BoujeeEnjinia1701/fieldnode/cad/drawings/FND-DWG-001.pdf

CONCEPT, NOT FOR FABRICATION | FieldNode · github.com/BoujeeEnjinia1701/fieldnode

FRONT VIEW
Scale 1:10; looking at the front (along +Y)

TOP VIEW
Scale 1:10; looking down (along -Z)

RIGHT VIEW
Scale 1:10; looking at the right side (along -X)

290

232 750

PRELIMINARY, NOT FOR FABRICATION

200

250 clamps

150

290 panel

915 MHZ WHIP (9)

PORTS A (LEFT) AND B, M12 5-PIN (10)

2 x M16 GLANDS (3)

POLE AXIS, 48.3 OD (40 TO 60)

NODE FACES -Y (TOWARD THE EQUATOR)

90

456

PANEL TILT 40 DEG

ISOMETRIC VIEW
Not to scale; grey pole stub is site supplied; seen from the front right and above, about 30 deg elevation

MAIN DIMENSIONS AND INTERFACES (MM)
Enclosure IP65 150 x 90 x 200 (W x D x H); base 1,750 above ground Panel 6 W 9 V class, 290 x 200, tilt 40 deg; top 2,206 above ground Panel overhangs lid by 57; front edge 121 above enclosure
Back plate 180 x 320 x 3 Al; V-blocks 60 x 33 x 20, 90 deg V
Band clamps 12 wide, 250 apart; poles 40 to 60 OD
Bracket bar 20 x 3: posts 161, struts 129 between holes Enclosure on 4 lugs, M5; bracket on 30 x 30 x 3 angle clips, M6
Bottom face: 2 rows, 27 and 55 in from the back face
Whip 915 MHz (US915), 190 long; tip 1,540 above ground
Option (14), not shown: shield 181 x 106 x 206, 15 gap, 4 thumb screws Ports A and B (10), M12 5-pin A-coded, pin positions per maker:
1 switched rail, 2 data A, 3 ground, 4 data B, 5 analog
Serial header (7) on the power board, pins 48 in from box front (lid off) Third-angle; front view from -Y; pole on Z axis; (n) = BOM line
REV | DESCRIPTION | DATE | BY
P1 | Preliminary GA for TRL 3 (from cad/src/model.py) | 2026-09-25 | AC
P2 | FND-DDR-002: 9 V class panel; sun shield option (14) | 2026-09-25 | AC
P3 | FND-DDR-003: design for construction | 2026-09-30 | AC
P4 | Port pinout, programming header (7), 915 MHz whip | 2026-10-02 | AC
FIELDNODE | github.com/BoujeeEnjinia1701/fieldnode

## General arrangement

DRAWING NO.
FND-DWG-001

REV
P4

SHEET
1 of 1

SIZE

## ANSI B

SCALE
1:10

UNITS
mm
PROJECTION | DATE
2026-10-02

DRAWN
Amish Chadha

MATERIAL / NOTES
Bought-in parts per bom/bom.csv; aluminium bracket and plate. PRELIMINARY, NOT FOR FABRICATION
Licensed CERN-OHL-S-2.0 · Design Molecule Lab · designmolecule.com | Generated from cad/src; do not edit by hand
