BoujeeEnjinia1701/fieldnode/cad/drawings/FND-DWG-101.pdf

### BUILD PLAN SKETCH, PLAN NOT YET BUILT FieldNode · github.com/BoujeeEnjinia1701/fieldnode

FRONT VIEW
Scale 1:5; looking at the front (along +Y)

TOP VIEW
Scale 1:5; looking down (along -Z)

RIGHT VIEW
Scale 1:5; looking at the right side (along -X)

180

3 320

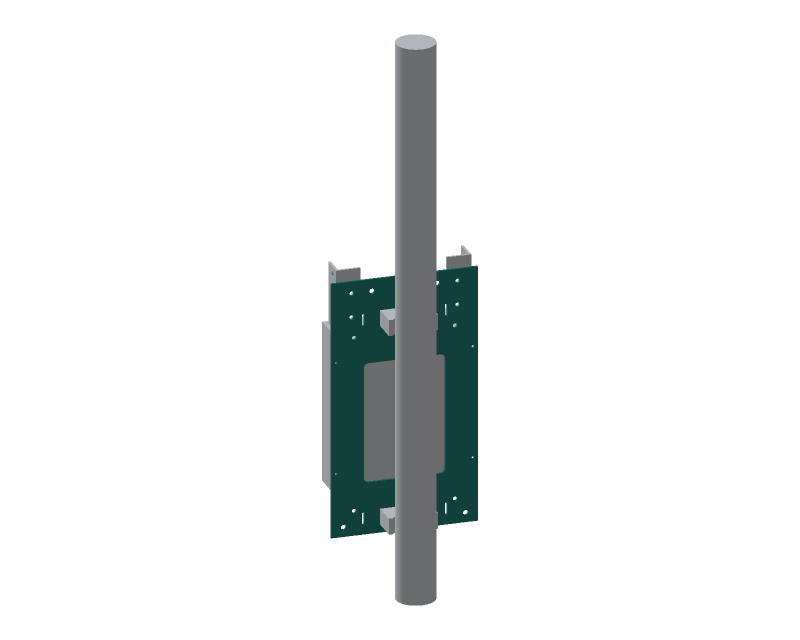
[picture p7: figure]

WHERE IT GOES
This part in colour, its neighbours in grey

HOW TO MAKE IT AND HOW IT FITS
Blank 180 x 320 mm, 3 mm aluminium. Front view is the face the box sits on. Heights from the bottom edge; sideways from the centre line.
Window 100 x 150 mm, 6 mm corner radius, 65 to 215 mm up: drill the corners 12 mm, cut between with a jigsaw, file straight.
Band slots 3 x 15 mm at 51 mm each side, centred 20 and 270 mm up: chain drill 3 mm, file square. The band goes through these.
V-block screws 4.5 mm at 18 mm each side, 20 and 270 mm up; countersink from the front so the screw heads sit flush.
Lug screws 5.5 mm at 62 mm each side, 31 and 249 mm up.
Plate clip screws 5.5 mm at 65 mm each side, 275 and 305 mm up.
Shield screws: drill 3.3 mm and tap M4 at 84 mm each side, 80 and 220 mm up. Wall holes 6.5 mm at 40 mm each side 305 mm up, 75 mm each side 12 mm up. Deburr every hole and edge; round the corners to about 2 mm.
Check: lay the V-blocks, lugs and clips on it and look through each hole.
REV | DESCRIPTION | DATE | BY
P1 | Making sketch for the prototype build plan | 2026-09-30 | AC
FIELDNODE | github.com/BoujeeEnjinia1701/fieldnode

## FieldNode back plate: making sketch

DRAWING NO.
FND-DWG-101

REV
P1

SHEET
1 of 1

SIZE

## ANSI B

SCALE
1:5

UNITS
mm
PROJECTION | DATE
2026-09-30

DRAWN
Amish Chadha

MATERIAL / NOTES
Aluminium sheet 3 mm, 5052 or 6061 class
Licensed CERN-OHL-S-2.0 · Design Molecule Lab · designmolecule.com | Generated from cad/src; do not edit by hand
