BoujeeEnjinia1701/fieldnode/cad/drawings/FND-DWG-102.pdf

### BUILD PLAN SKETCH, PLAN NOT YET BUILT FieldNode · github.com/BoujeeEnjinia1701/fieldnode

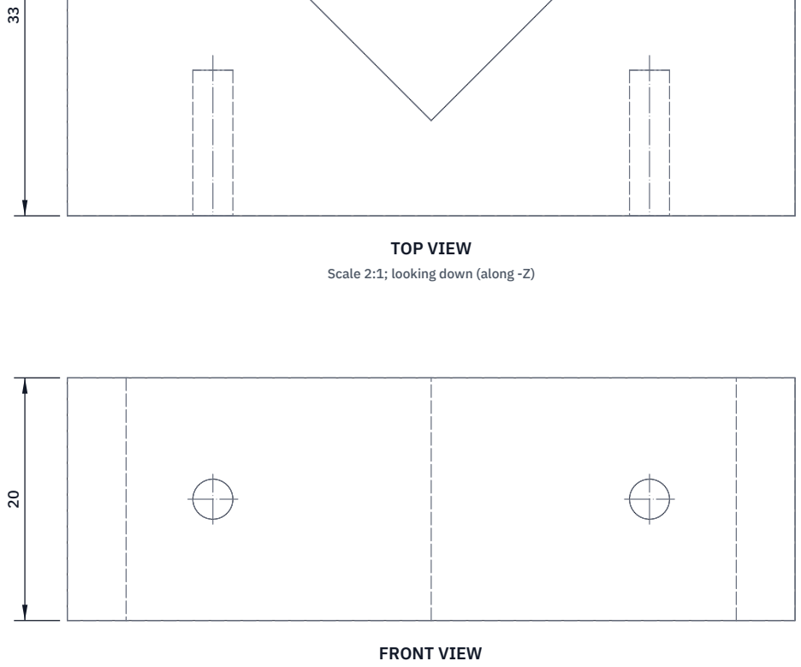
[picture p8: figure]
FRONT VIEW; TOP VIEW; Scale 2:1; looking down (along -Z)

Scale 2:1; looking at the front (along +Y)

RIGHT VIEW
Scale 2:1; looking at the right side (along -X)

60

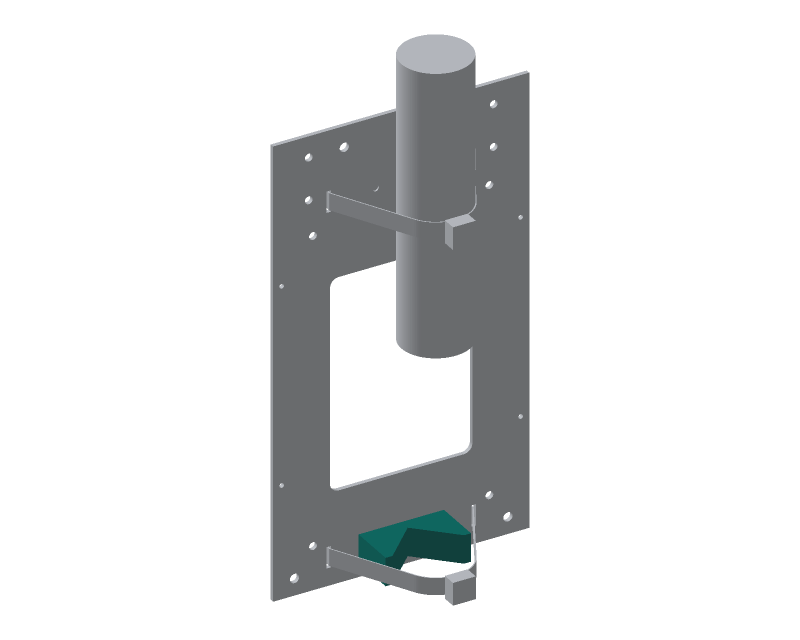
[picture p9: figure]

WHERE IT GOES
This part in colour, its neighbours in grey

HOW TO MAKE IT AND HOW IT FITS
Make two. Saw a 20 mm slice off 60 x 40 mm bar; saw and file it to 60 wide x 33 deep x 20 tall. The flat back goes on the back plate. Scribe a 90 degree V on both 60 x 33 faces with a 45 degree square: 50.3 mm wide at the front face, point 7.8 mm from the back face. Saw just inside both lines, file to the lines, keep the V faces flat. Break the V's sharp front edges 0.5 mm so they cannot score the pole. Drill 3.3 mm, 14 mm deep, and tap M4 12 deep in the back face,
at 18 mm each side of centre, half way up (10 mm).
Fit: two M4 countersunk screws from the front of the plate.
The 48.3 mm pole touches both V faces 24.9 mm from the plate, about 8 mm inside the front face. 40 to 60 mm poles also seat. Check: on a 48 mm tube the block must not rock; hold it to light, light should show at the bottom of the V, not along the faces.
REV | DESCRIPTION | DATE | BY
P1 | Making sketch for the prototype build plan | 2026-09-30 | AC
FIELDNODE | github.com/BoujeeEnjinia1701/fieldnode

## FieldNode V-block (make 2): making sketch

DRAWING NO.
FND-DWG-102

REV
P1

SHEET
1 of 1

SIZE

## ANSI B

SCALE
2:1

UNITS
mm
PROJECTION | DATE
2026-09-30

DRAWN
Amish Chadha

MATERIAL / NOTES
Aluminium flat bar 60 x 40 mm, 6082 or 6061
Licensed CERN-OHL-S-2.0 · Design Molecule Lab · designmolecule.com | Generated from cad/src; do not edit by hand
