BoujeeEnjinia1701/fieldnode/cad/drawings/FND-DWG-103.pdf

### BUILD PLAN SKETCH, PLAN NOT YET BUILT FieldNode · github.com/BoujeeEnjinia1701/fieldnode

FRONT VIEW
Scale 1:1; looking at the front (along +Y)

TOP VIEW
Scale 1:1; looking down (along -Z)

RIGHT VIEW
Scale 1:1; looking at the right side (along -X)

30

30 77

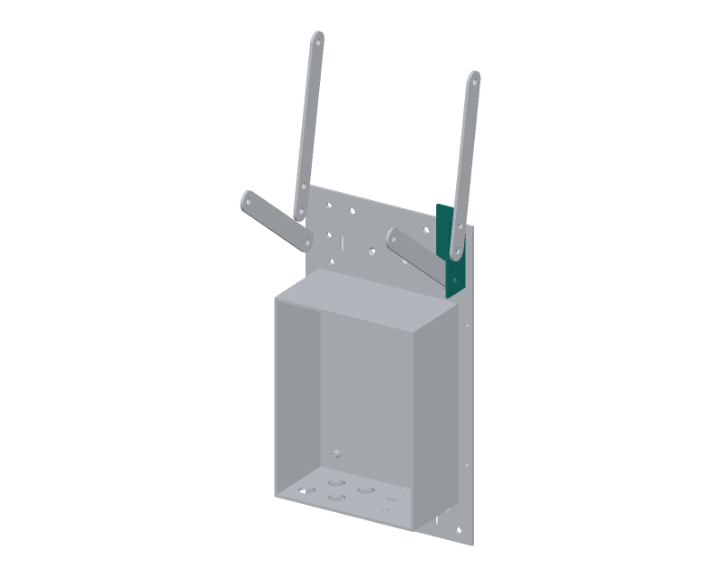
[picture p10: figure]

WHERE IT GOES
This part in colour, its neighbours in grey

HOW TO MAKE IT AND HOW IT FITS
Cut two 77 mm lengths of 30 x 30 x 3 angle; square and deburr the ends. Flat leg (goes on the plate): two 5.5 mm holes, 12 mm in from its free edge, 17 and 47 mm up from the bottom end.
Upright leg (stands forward): three 6.6 mm holes, measured from the back of the angle (the face on the plate) and up from the bottom end: strut foot 17 back, 14 up; post 18 back, 44 up; post 13.7 back, 67.6 up. Right and left clips are mirror images: drill the upright legs as a
pair clamped back to back so the holes line up.
Fit: flat leg on the plate front, upright leg 80 to 83 mm from the
centre line, bottom end 258 mm up the plate; M5 screws from behind. The post bolts to the outside of the upright leg, the strut to the inside. Check: the clip sits flat on the plate and its upright leg is square.
REV | DESCRIPTION | DATE | BY
P1 | Making sketch for the prototype build plan | 2026-09-30 | AC
FIELDNODE | github.com/BoujeeEnjinia1701/fieldnode

## FieldNode plate clip (make 2, a left and a right): making sketch

DRAWING NO.
FND-DWG-103

REV
P1

SHEET
1 of 1

SIZE

## ANSI B

SCALE
1:1

UNITS
mm
PROJECTION | DATE
2026-09-30

DRAWN
Amish Chadha

MATERIAL / NOTES
Aluminium equal angle 30 x 30 x 3 mm
Licensed CERN-OHL-S-2.0 · Design Molecule Lab · designmolecule.com | Generated from cad/src; do not edit by hand
