BoujeeEnjinia1701/fieldnode/cad/drawings/FND-DWG-104.pdf

### BUILD PLAN SKETCH, PLAN NOT YET BUILT FieldNode · github.com/BoujeeEnjinia1701/fieldnode

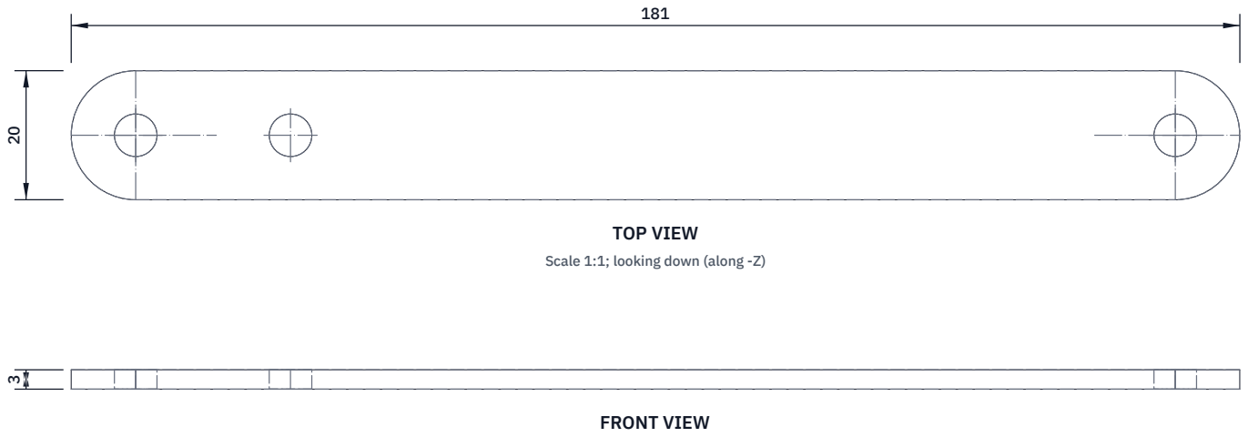
[picture p11: figure]
FRONT VIEW; TOP VIEW; Scale 1:1; looking down (along -Z)

Scale 1:1; looking at the front (along +Y)

RIGHT VIEW
Scale 1:1; looking at the right side (along -X)

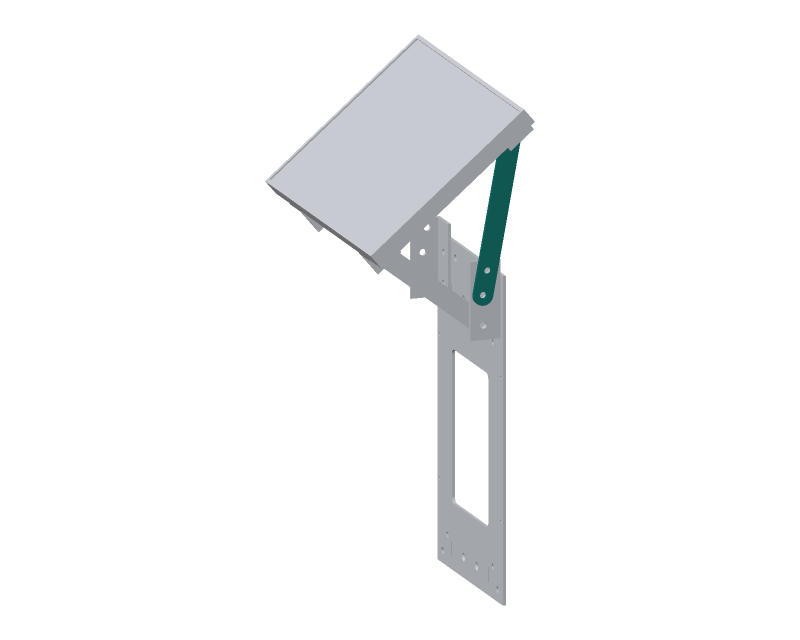
[picture p12: figure]

WHERE IT GOES
This part in colour, its neighbours in grey

HOW TO MAKE IT AND HOW IT FITS
Cut two 181 mm lengths of 20 x 3 mm flat bar.
Round both ends to a 10 mm radius (file to a scribed circle).
Drill 6.6 mm: one hole 10 mm from each end (161.2 mm apart) and a third 24 mm from the lower hole, on the centre line.
Drill the two posts clamped together so the holes match.
Fit: the lower end bolts to the outside of the plate clip with two M6 bolts, which hold the post rigid. The upper end bolts to the high
panel clip with one M6 bolt, which is the panel's hinge.
The post leans back 10 degrees from vertical and passes 2 mm in front of the plate's top edge.
Check: hole centres 161 mm and 24 mm apart, within 0.5 mm.
REV | DESCRIPTION | DATE | BY
P1 | Making sketch for the prototype build plan | 2026-09-30 | AC
FIELDNODE | github.com/BoujeeEnjinia1701/fieldnode

## FieldNode post (make 2): making sketch

DRAWING NO.
FND-DWG-104

REV
P1

SHEET
1 of 1

SIZE

## ANSI B

SCALE
1:1

UNITS
mm
PROJECTION | DATE
2026-09-30

DRAWN
Amish Chadha

MATERIAL / NOTES
Aluminium flat bar 20 x 3 mm, 6063 class
Licensed CERN-OHL-S-2.0 · Design Molecule Lab · designmolecule.com | Generated from cad/src; do not edit by hand
