BoujeeEnjinia1701/fieldnode/cad/drawings/FND-DWG-105.pdf

### BUILD PLAN SKETCH, PLAN NOT YET BUILT FieldNode · github.com/BoujeeEnjinia1701/fieldnode

FRONT VIEW
Scale 1:1; looking at the front (along +Y)

TOP VIEW
Scale 1:1; looking down (along -Z)

RIGHT VIEW
Scale 1:1; looking at the right side (along -X)

149

20 3

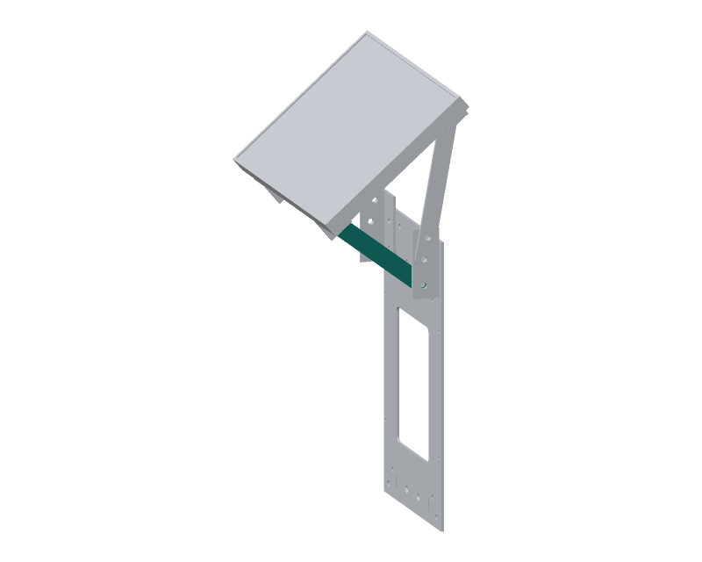
[picture p13: figure]

WHERE IT GOES
This part in colour, its neighbours in grey

HOW TO MAKE IT AND HOW IT FITS
Cut two 149 mm lengths of 20 x 3 mm flat bar.
Round both ends to a 10 mm radius.
Drill 6.6 mm, 10 mm from each end: 129.2 mm between centres. This length sets the panel tilt of 40 degrees.
Drill the two struts clamped together so the holes match.
Fit: the lower end bolts to the inside of the plate clip, the upper
end to the inside of the low panel clip; one M6 bolt each end.
The strut rises at 38 degrees and passes 10 mm above the sun shield. Check: hole centres 129.2 mm apart, within 0.5 mm; a shorter strut tips the panel steeper, a longer one flatter.
REV | DESCRIPTION | DATE | BY
P1 | Making sketch for the prototype build plan | 2026-09-30 | AC
FIELDNODE | github.com/BoujeeEnjinia1701/fieldnode

## FieldNode strut (make 2): making sketch

DRAWING NO.
FND-DWG-105

REV
P1

SHEET
1 of 1

SIZE

## ANSI B

SCALE
1:1

UNITS
mm
PROJECTION | DATE
2026-09-30

DRAWN
Amish Chadha

MATERIAL / NOTES
Aluminium flat bar 20 x 3 mm, 6063 class
Licensed CERN-OHL-S-2.0 · Design Molecule Lab · designmolecule.com | Generated from cad/src; do not edit by hand
