BoujeeEnjinia1701/fieldnode/cad/drawings/FND-DWG-106.pdf

### BUILD PLAN SKETCH, PLAN NOT YET BUILT FieldNode · github.com/BoujeeEnjinia1701/fieldnode

FRONT VIEW
Scale 2:1; looking at the front (along +Y)

TOP VIEW
Scale 2:1; looking down (along -Z)

RIGHT VIEW
Scale 2:1; looking at the right side (along -X)

30

30 30

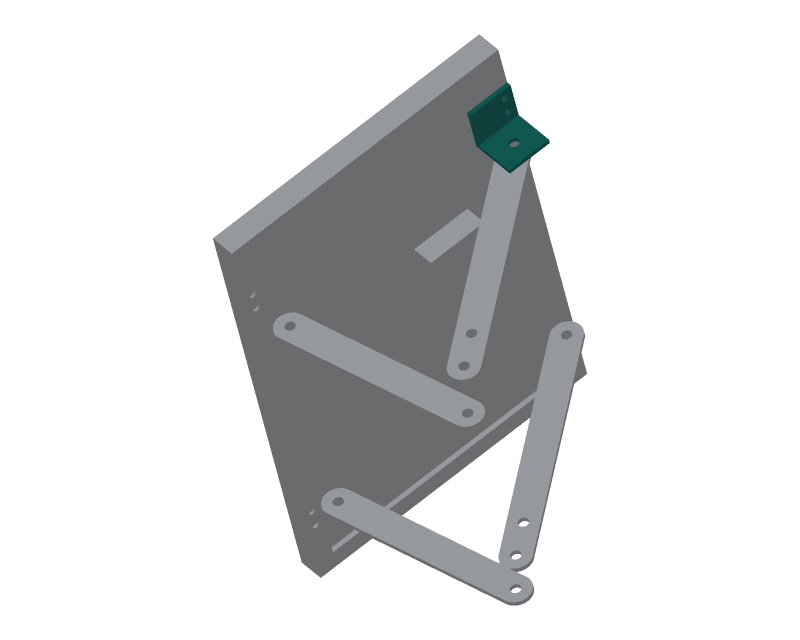
[picture p14: figure]

WHERE IT GOES
This part in colour, its neighbours in grey

HOW TO MAKE IT AND HOW IT FITS
Cut four 30 mm lengths of 30 x 30 x 3 angle; deburr.
Flat leg (goes on the panel frame's back lip): two 4.5 mm holes,
6 mm from one end, 11 and 23 mm from the back of the upright leg. Upright leg: one 6.6 mm hole at mid-length (15 mm), 16.5 mm out from the face that sits on the lip.
All four clips are the same. On each side one goes at the panel's high edge (post), one at its low edge (strut); the drilled end lines up
with the panel edge, the flat leg points outward.
Fit: M4 bolts through the clip and the frame lip, nut inside the frame. Drill the lip through the clip; keep clear of the glass and cells.
Check the panel you buy has a back lip at least 12 mm wide;
if not, stop and choose clips to suit before drilling.
REV | DESCRIPTION | DATE | BY
P1 | Making sketch for the prototype build plan | 2026-09-30 | AC
P2 | Lip check note no longer points to an open question | 2026-10-02 | AC
FIELDNODE | github.com/BoujeeEnjinia1701/fieldnode

## FieldNode panel clip (make 4): making sketch

DRAWING NO.
FND-DWG-106

REV
P2

SHEET
1 of 1

SIZE

## ANSI B

SCALE
2:1

UNITS
mm
PROJECTION | DATE
2026-10-02

DRAWN
Amish Chadha

MATERIAL / NOTES
Aluminium equal angle 30 x 30 x 3 mm
Licensed CERN-OHL-S-2.0 · Design Molecule Lab · designmolecule.com | Generated from cad/src; do not edit by hand
