BoujeeEnjinia1701/fieldnode/cad/drawings/FND-DWG-107.pdf

### BUILD PLAN SKETCH, PLAN NOT YET BUILT FieldNode · github.com/BoujeeEnjinia1701/fieldnode

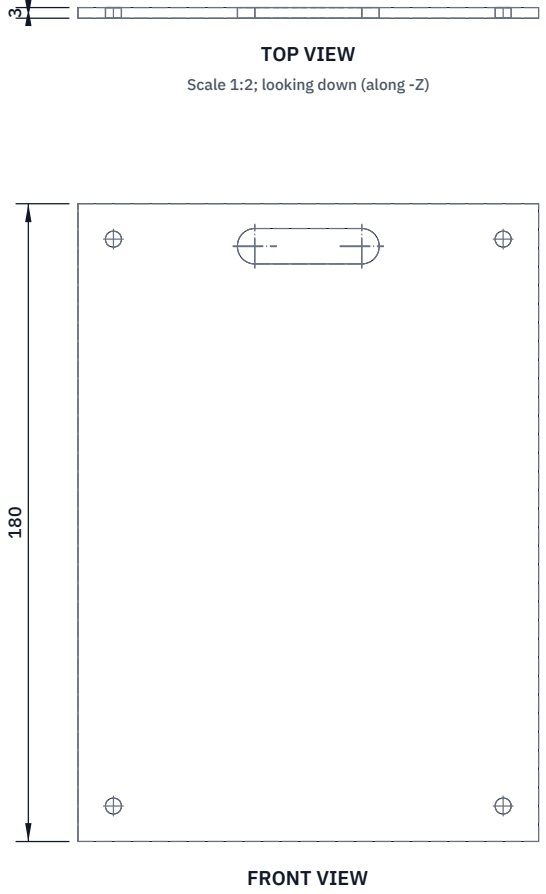
[picture p15: figure]
FRONT VIEW; TOP VIEW; Scale 1:2; looking down (along -Z)

Scale 1:2; looking at the front (along +Y)

RIGHT VIEW
Scale 1:2; looking at the right side (along -X)

130

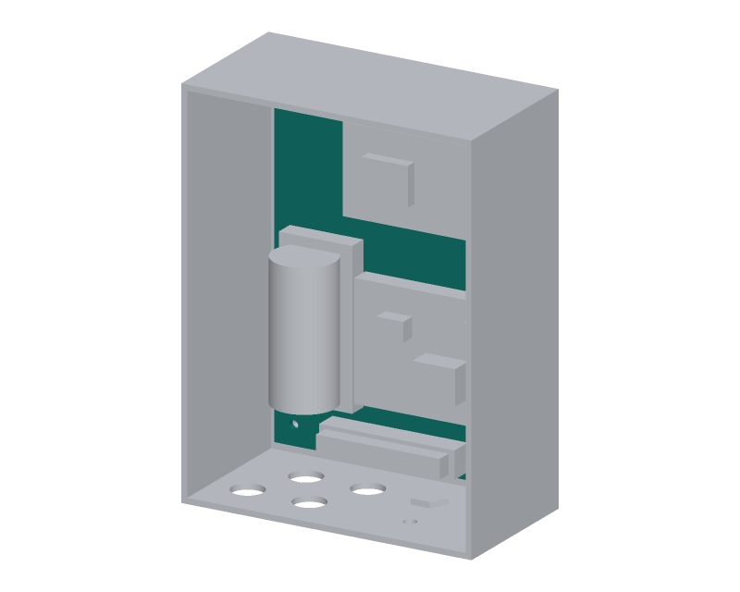
[picture p16: figure]

WHERE IT GOES
This part in colour, its neighbours in grey

HOW TO MAKE IT AND HOW IT FITS
Print flat, 130 x 180 x 3 mm, in ASA in an enclosed printer.
Four 4.5 mm holes 10 mm in from each side and from top and bottom (110 x 160 mm apart), to match the enclosure's four moulded bosses. Measure your enclosure's bosses first and move the holes to suit. Finger slot 40 x 10 mm, 7 mm below the top edge, for lifting out.
Lay out on the front: cell holder lower left, power modules lower right (programming header at their top right, pins toward the lid), controller above, connector strip along the bottom edge.
Mark each module's holes through the module; drill 3.2 mm for M3 screws on 6 mm nylon standoffs.
Fit: four M4 screws into the bosses; the plate sits 6 mm off the back wall and 7 mm above the floor, clear of the gland nuts.
Check: flat within 0.5 mm; drops in and lifts out without force.
REV | DESCRIPTION | DATE | BY
P1 | Making sketch for the prototype build plan | 2026-09-30 | AC
P2 | Programming header on the power board (FND-DEC-001) | 2026-10-02 | AC
FIELDNODE | github.com/BoujeeEnjinia1701/fieldnode

## FieldNode internal plate: making sketch

DRAWING NO.
FND-DWG-107

REV
P2

SHEET
1 of 1

SIZE

## ANSI B

SCALE
1:2

UNITS
mm
PROJECTION | DATE
2026-10-02

DRAWN
Amish Chadha

MATERIAL / NOTES
ASA, 3D printed, 100 % infill
Licensed CERN-OHL-S-2.0 · Design Molecule Lab · designmolecule.com | Generated from cad/src; do not edit by hand
