BoujeeEnjinia1701/fieldnode/cad/drawings/FND-DWG-108.pdf

### BUILD PLAN SKETCH, PLAN NOT YET BUILT FieldNode · github.com/BoujeeEnjinia1701/fieldnode

FRONT VIEW
Scale 1:5; looking at the front (along +Y)

TOP VIEW
Scale 1:5; looking down (along -Z)

RIGHT VIEW
Scale 1:5; looking at the right side (along -X)

150

78 200

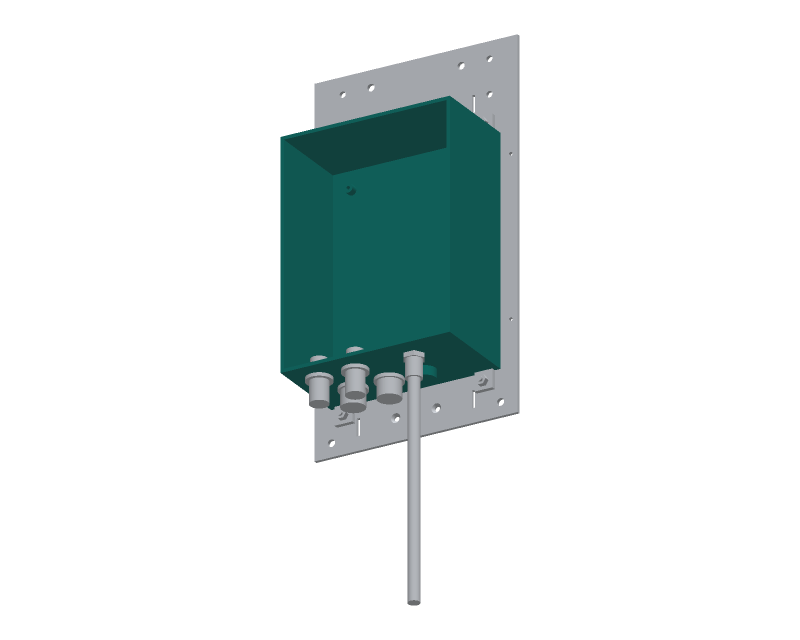
[picture p17: figure]

WHERE IT GOES
This part in colour, its neighbours in grey

HOW TO MAKE IT AND HOW IT FITS
Drawn upside down: stand the box on its top, back face toward you; the top view then shows the bottom face as you see it on the bench. Measure from the back face, and sideways from the centre line (left and right as seen from the front). The drilling layout picture repeats this. Back row, 27 mm from the back face: gland 1 at 40 left, gland 2 at
8 left (16.2 mm holes), vent at 24 right (12.2 mm).
Front row, 55 mm from the back face: port A at 54 left, port B at
22 left (16.2 mm), antenna at 30 right (6.5 mm).
Every outside flange is at least 8 mm from the next one.
Tape the face, pilot drill 3 mm slowly with wood behind, open out with a step drill, light pressure. No solvents: polycarbonate crazes.
Deburr inside and out. Check each hole size on the part's datasheet before the last step of the drill.
Fit the lugs (the maker's kit) to the four back corners as the maker says.
REV | DESCRIPTION | DATE | BY
P1 | Making sketch for the prototype build plan | 2026-09-30 | AC
FIELDNODE | github.com/BoujeeEnjinia1701/fieldnode

## FieldNode enclosure body: drilling sketch

DRAWING NO.
FND-DWG-108

REV
P1

SHEET
1 of 1

SIZE

## ANSI B

SCALE
1:5

UNITS
mm
PROJECTION | DATE
2026-09-30

DRAWN
Amish Chadha

MATERIAL / NOTES
Bought IP65 polycarbonate box 150 x 90 x 200 mm
Licensed CERN-OHL-S-2.0 · Design Molecule Lab · designmolecule.com | Generated from cad/src; do not edit by hand
