BoujeeEnjinia1701/fieldnode/cad/drawings/FND-DWG-109.pdf

### BUILD PLAN SKETCH, PLAN NOT YET BUILT FieldNode · github.com/BoujeeEnjinia1701/fieldnode

FRONT VIEW
Scale 1:5; looking at the front (along +Y)

TOP VIEW
Scale 1:5; looking down (along -Z)

RIGHT VIEW
Scale 1:5; looking at the right side (along -X)

182

106 206

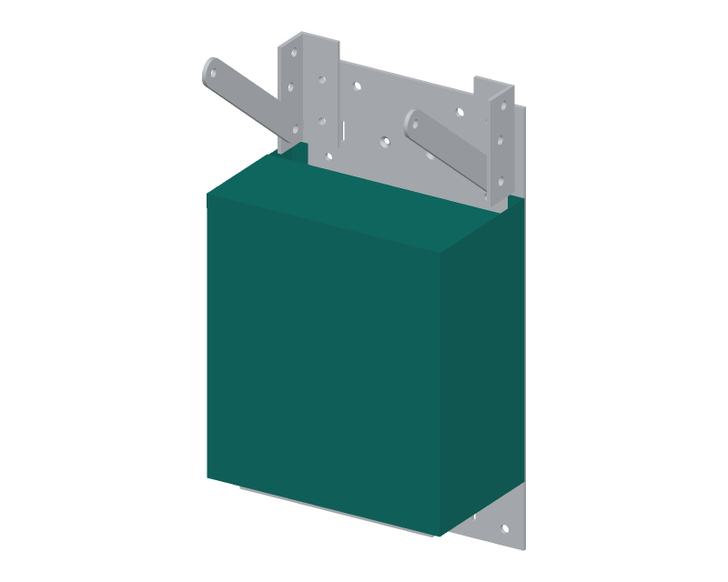
[picture p18: figure]

WHERE IT GOES
This part in colour, its neighbours in grey

HOW TO MAKE IT AND HOW IT FITS
One blank, folded: front 181 x 206 mm in the middle; a side 106 mm wide on each long edge; a top 76 mm deep on the top edge (the 30 mm vent slot at the back is simply the top being short); 10 mm tabs
on the ends of the top; a 12 mm flange on the back of each side.
Cut with snips; drill 3 mm relief holes where bend lines cross.
Fold the sides back 90 degrees, then the top, then the tabs down over the sides; rivet each tab with two 3.2 mm rivets.
Fold each flange 90 degrees inward; drill two 4.5 mm holes 6 mm from the fold, 30 and 170 mm up from the lower edge.
Fit: flanges flat on the plate, 3 mm beside the box; four M4 thumb screws into the plate. 15 mm air gap on the front, sides and top.
To open the lid: undo the four thumb screws, pull the shield forward. Check: the gap is 15 mm (plus or minus 2) all round.
REV | DESCRIPTION | DATE | BY
P1 | Making sketch for the prototype build plan | 2026-09-30 | AC
FIELDNODE | github.com/BoujeeEnjinia1701/fieldnode

## FieldNode sun shield (hot sites only): making sketch

DRAWING NO.
FND-DWG-109

REV
P1

SHEET
1 of 1

SIZE

## ANSI B

SCALE
1:5

UNITS
mm
PROJECTION | DATE
2026-09-30

DRAWN
Amish Chadha

MATERIAL / NOTES
White powder-coated aluminium sheet 0.5 mm
Licensed CERN-OHL-S-2.0 · Design Molecule Lab · designmolecule.com | Generated from cad/src; do not edit by hand
