BoujeeEnjinia1701/fieldnode/cad/drawings/FND-DWG-001.png

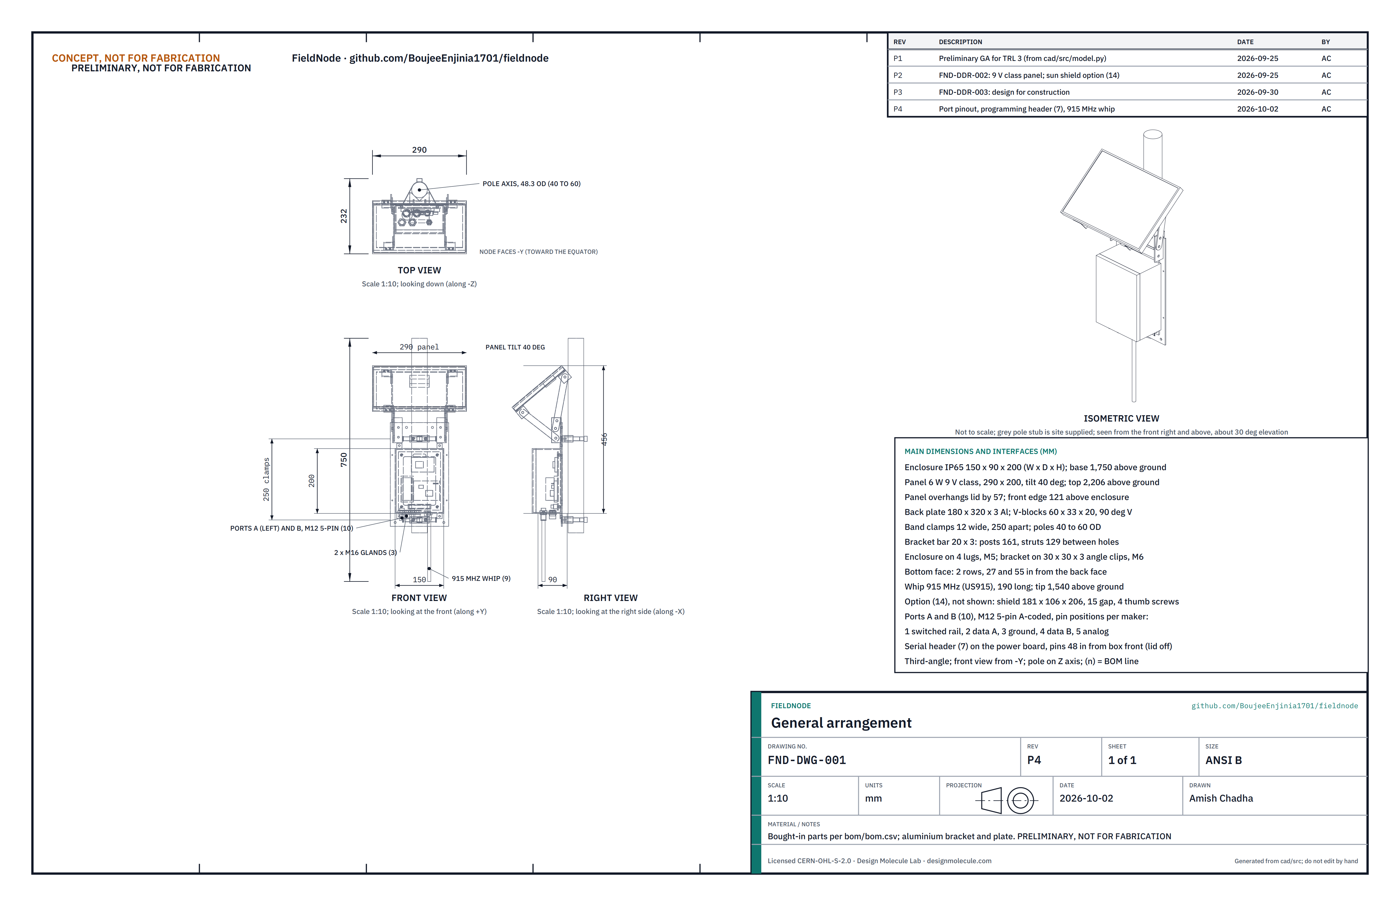
cad/drawings/FND-DWG-001.png
