BoujeeEnjinia1701/fieldnode/media/card.png

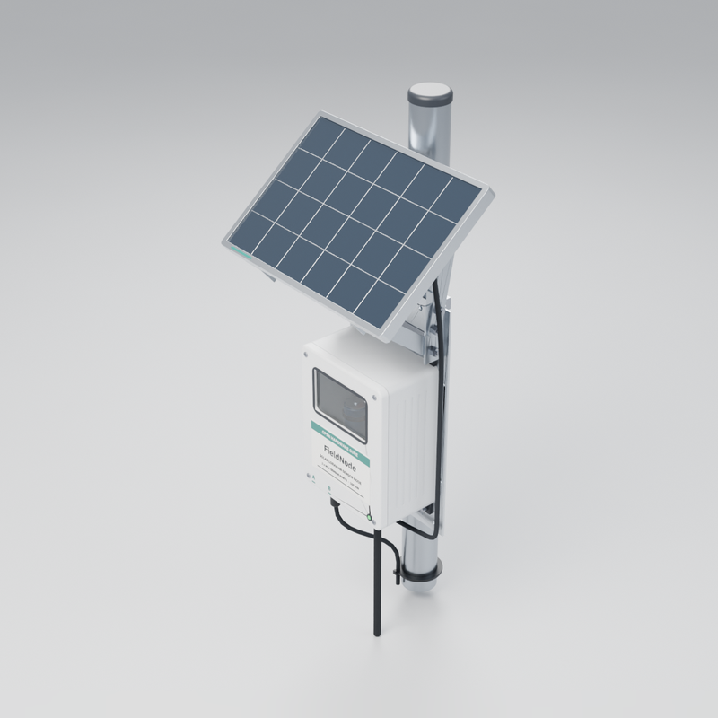
media/card.png
