BoujeeEnjinia1701/fieldnode/media/render-detail.png

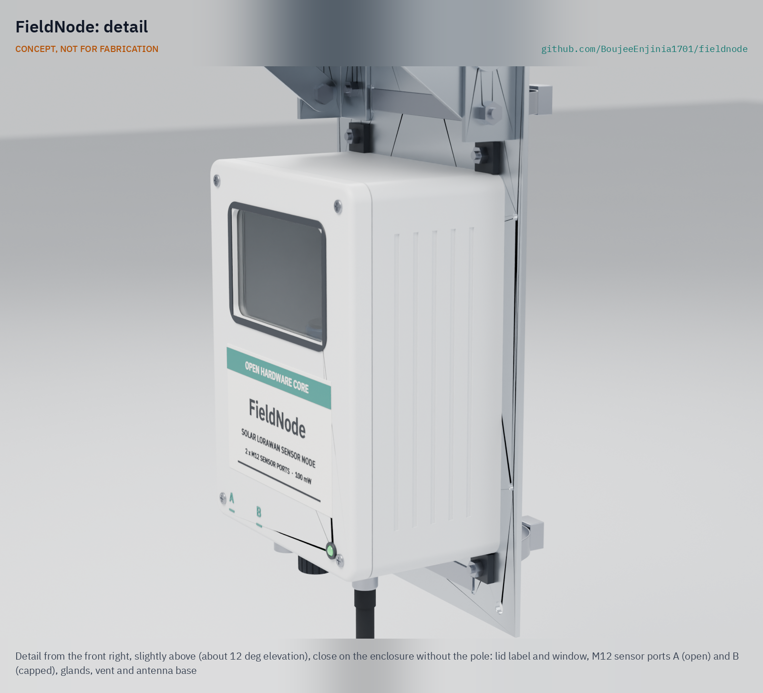
media/render-detail.png
