BoujeeEnjinia1701/fieldnode/media/render-exploded.png

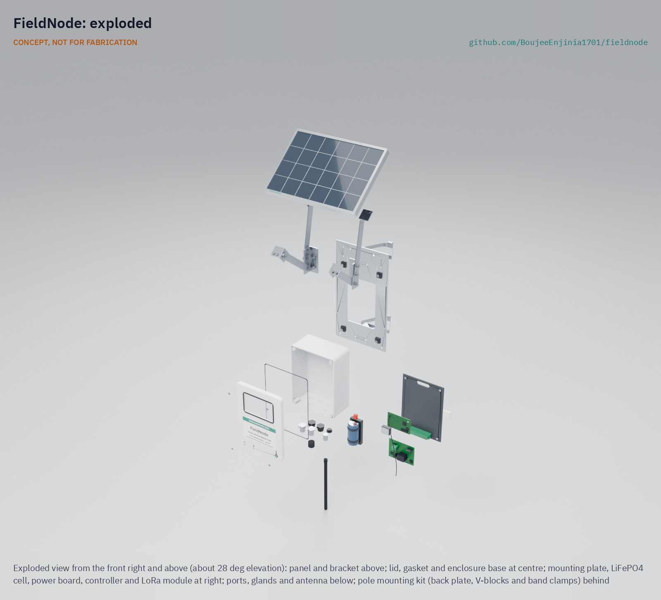
media/render-exploded.png
