BoujeeEnjinia1701/fieldnode/media/social-preview.png

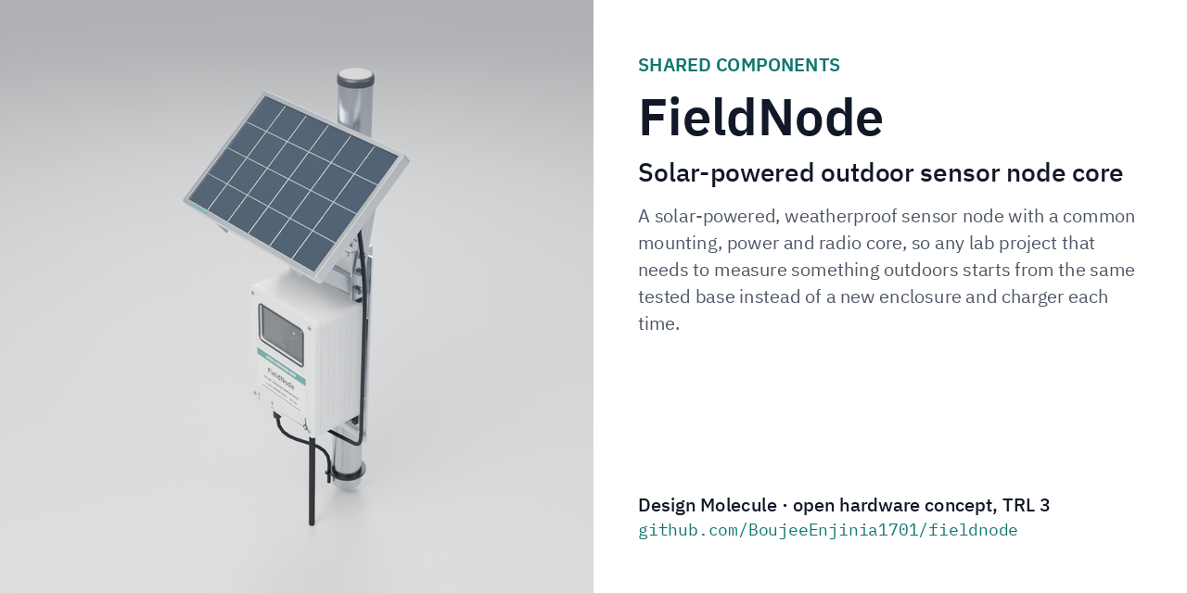
media/social-preview.png
